rbello/Minitel-Raspberry-Retro-gaming/Electronique/gOFnCZM.jpg

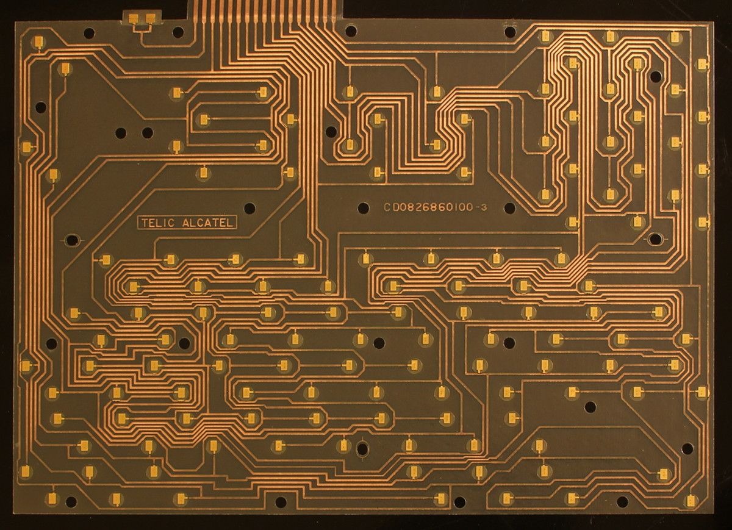
Electronique/gOFnCZM.jpg
